GiuseppeSpathis/SvegliaSordi/utilsRelazione/codeBlocks1.PNG

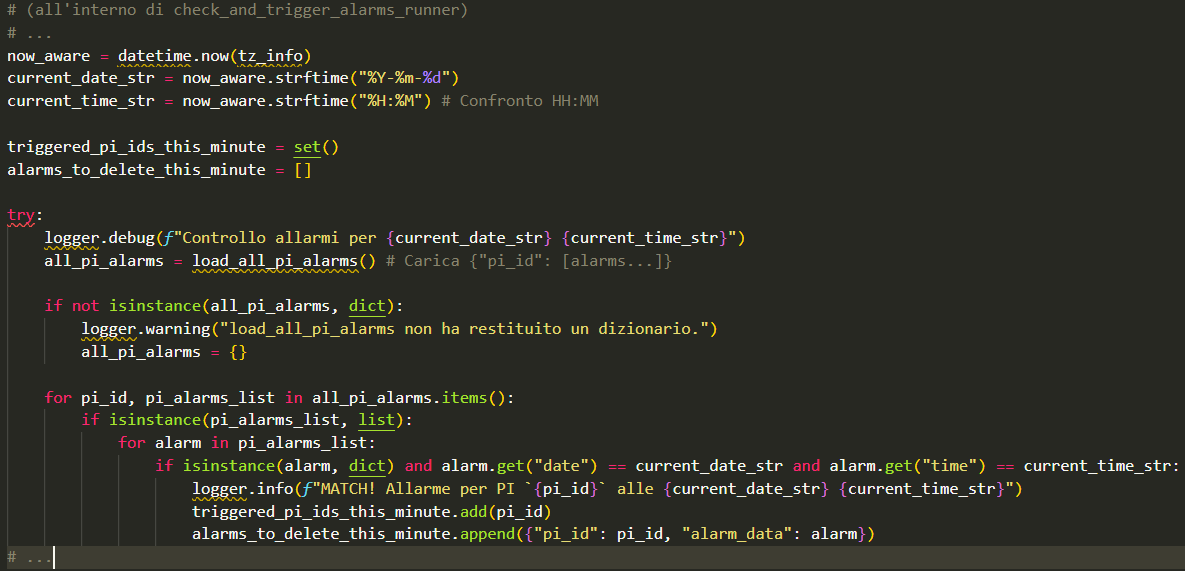
utilsRelazione/codeBlocks1.PNG
