GiuseppeSpathis/SvegliaSordi/utilsRelazione/codeBlocks2.PNG

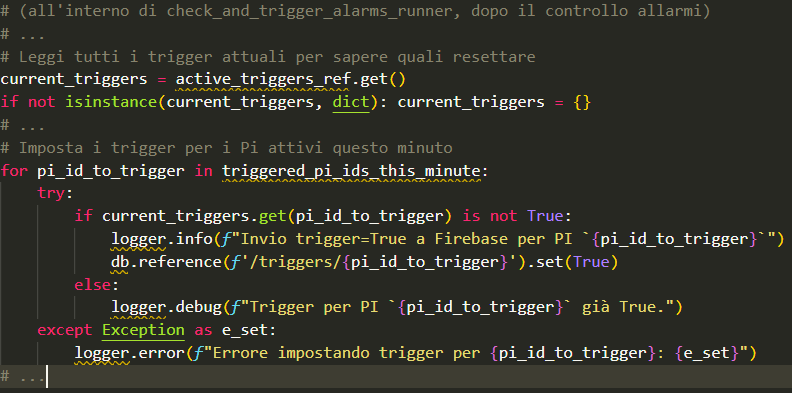
utilsRelazione/codeBlocks2.PNG
