GiuseppeSpathis/SvegliaSordi/utilsRelazione/codeBlocks3.PNG

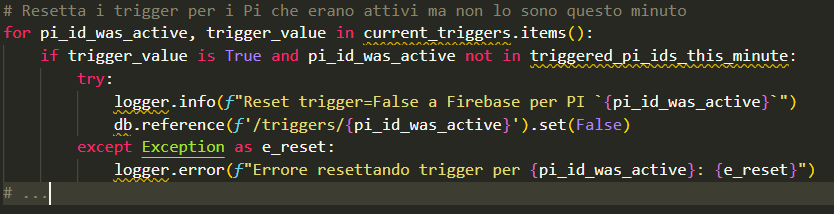
utilsRelazione/codeBlocks3.PNG
