GiuseppeSpathis/SvegliaSordi/utilsRelazione/firebase.PNG

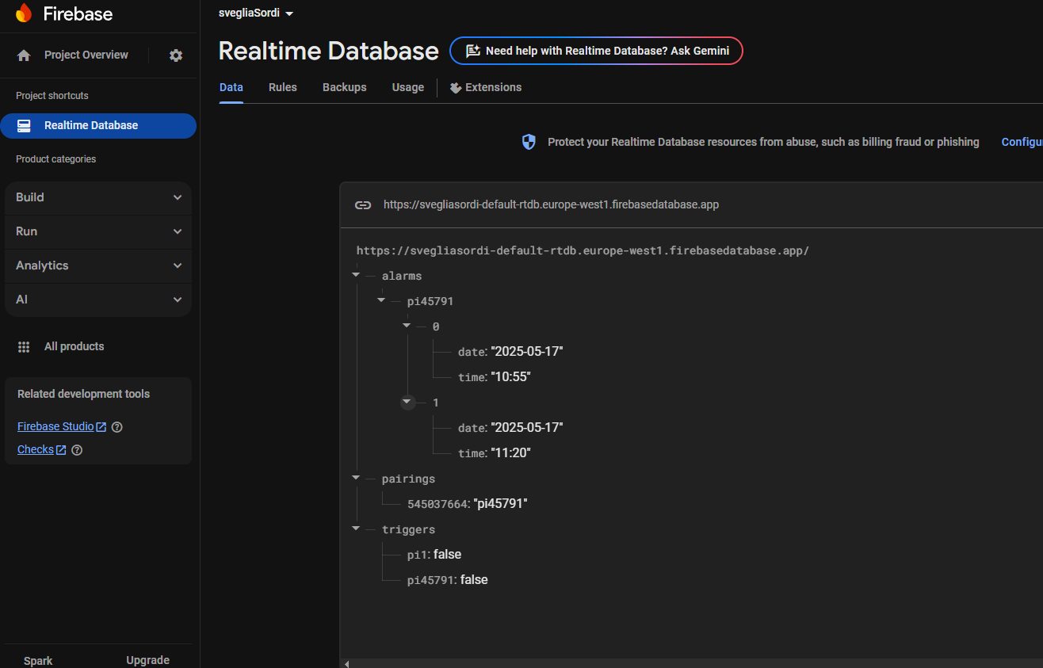
utilsRelazione/firebase.PNG
