GiuseppeSpathis/SvegliaSordi/utilsRelazione/fusion360Esempio.PNG

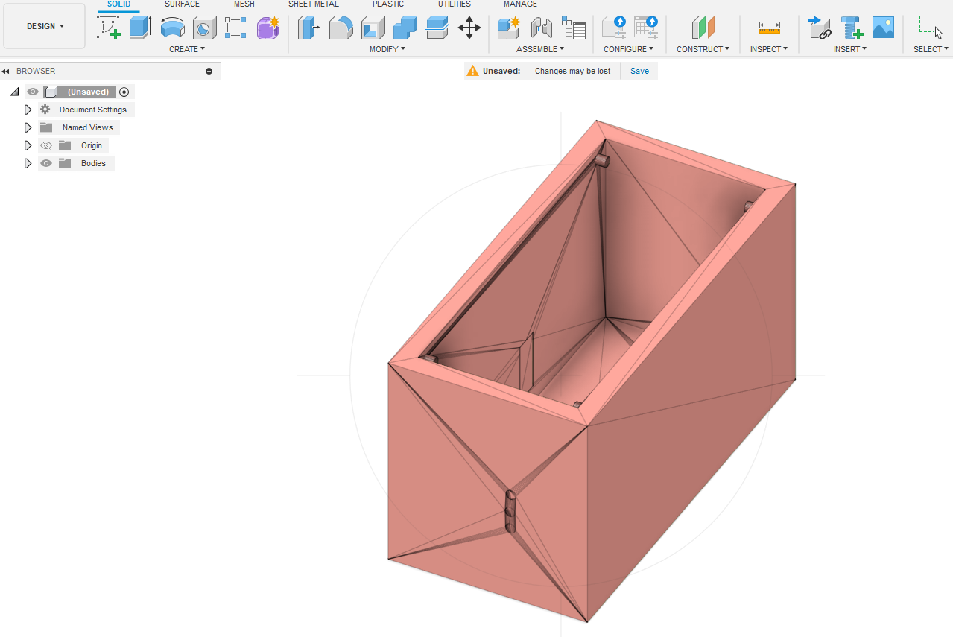
utilsRelazione/fusion360Esempio.PNG
