GiuseppeSpathis/SvegliaSordi/utilsRelazione/leds_fritzing.png

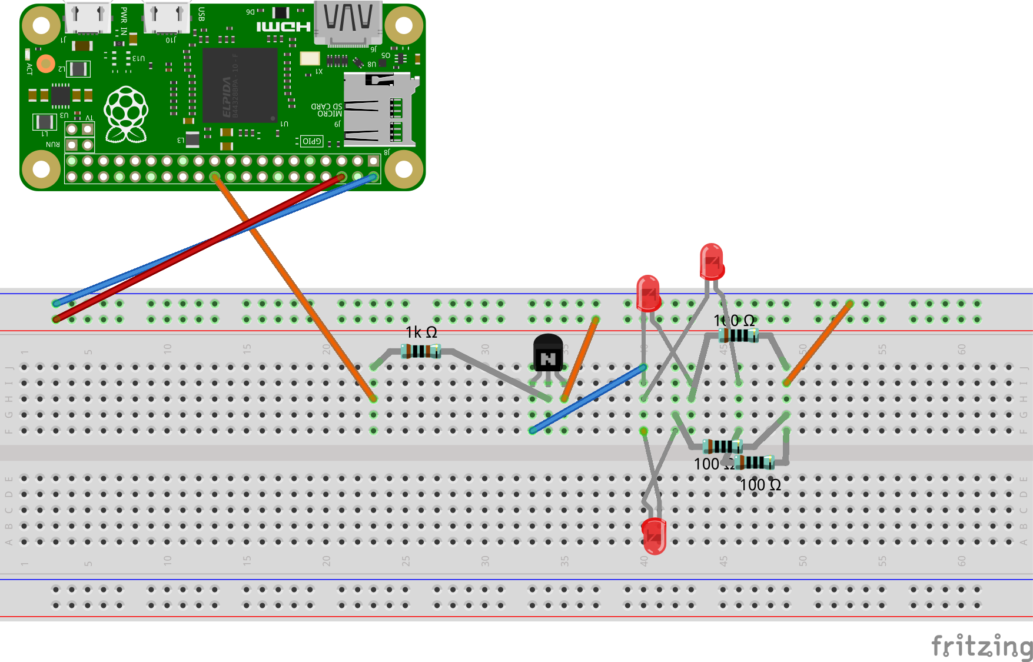
utilsRelazione/leds_fritzing.png
