GiuseppeSpathis/SvegliaSordi/utilsRelazione/progettoCompleto.jpg

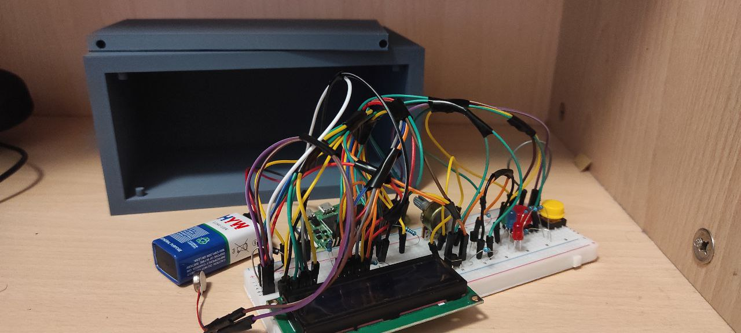
utilsRelazione/progettoCompleto.jpg
